btondin/PROJ_CLOCK_16C745/VFDCLK.X/vfd.c

/**
 * =====================================================================
 *  vfd.c — Driver do display VFD IEE Century Series 036X2 (20x2)
 * =====================================================================
 *  Referência: "Specification, VFD, Century Series, Dot Matrix
 *  Modules" (IEE S036X2, rev. N):
 *    - seção 3.2.2.1: interface serial (19200 8N1)
 *    - seção 3.3    : tempos de execução (tabela 3-5) e power-up 500 ms
 *    - seção 4      : códigos de programação usados aqui:
 *        14h  reset por software (limpa tela, modos e atributos)
 *        15h  limpa a tela e leva o cursor ao início ("home")
 *        0Eh  cursor invisível
 *        1Bh  posiciona cursor (2 bytes: 1Bh + ID da posição 0..39)
 *        19h  "Set Address Bit 0 High": em modo serial, equivale a
 *             levantar a linha A0 SOMENTE para o próximo byte — é o
 *             mecanismo para alcançar os códigos 30h..3Fh (seção 4.6)
 *        30h  brilho (3 bytes: 30h, coluna [FFh = todas], nível 0..7)
 *
 *  Por que não há esperas por BUSY: em serial cada byte ocupa 521 us
 *  de linha (19200 baud) e os comandos usados em regime ("Send
 *  Character" e "Cursor Locate") levam ~170 us — o próprio baud rate
 *  serve de flow control. Os comandos lentos (Clear, Reset) só ocorrem
 *  em vfd_iniciar(), que aguarda explicitamente.
 *
 *  A transmissão usa a macro UART_TX (e não a função uart_enviar)
 *  para não gastar níveis da pilha de hardware de 8 posições — as
 *  funções deste driver são chamadas pelo main já no 3º nível.
 * =====================================================================
 */
#include <xc.h>
#include "board.h"
#include "uart.h"
#include "vfd.h"

/* Códigos de controle do IEE 036X2 (A0/RS baixo, seção 4.1)          */
#define VFD_CMD_CURSOR_OFF      0x0Eu
#define VFD_CMD_RESET_SW        0x14u
#define VFD_CMD_LIMPAR_HOME     0x15u
#define VFD_CMD_HOME            0x16u   /* cursor ao início, sem limpar */
#define VFD_CMD_POSICIONAR      0x1Bu
#define VFD_CMD_PREFIXO_A0      0x19u   /* A0=1 só para o próximo byte */
#define VFD_CMD_DEFINIR_UDC     0x18u   /* define caractere (7 bytes)  */

/* Códigos de controle com A0 alto (seção 4.5, exigem prefixo 19h)    */
#define VFD_CMD_BRILHO          0x30u
#define VFD_BRILHO_TODAS_COLS   0xFFu
#define VFD_CMD_BLINK_INICIO    0x31u   /* + código de taxa (2 bytes)  */
#define VFD_CMD_BLINK_FIM       0x32u

/* ------------------------------------------------------------------
 * "Respiro" após o comando de posicionamento (1Bh + posição)
 * ------------------------------------------------------------------
 * O USART do PIC transmite BACK-TO-BACK (o buffer duplo TXREG->TSR
 * emenda um byte no outro, sem intervalo). O display IEE, depois de
 * receber "mover cursor" (1Bh + posição), fica ocupado ~1..1,5 ms
 * executando o movimento e, nesse meio-tempo, PERDE os primeiros
 * caracteres enviados em seguida (ou os marca com '#', o símbolo de
 * erro de recepção — spec 3.2.2.1). Foi por isso que o teste manual
 * pelo PL2303 (bytes digitados com pausas) funcionou e a transmissão
 * contínua do PIC não. Este atraso curto dá tempo ao display antes de
 * mandar os dados. O streaming de caracteres em si aguenta 19200
 * back-to-back (Send Character ~170 us < 521 us/byte).               */
#define VFD_ATRASO_POS_MS   3

#define VFD_IR_PARA(pos)                          \
    do {                                          \
        UART_TX(VFD_CMD_POSICIONAR);              \
        UART_TX((uint8_t)(pos));                  \
        __delay_ms(VFD_ATRASO_POS_MS);            \
    } while (0)

/* ------------------------------------------------------------------
 * CARACTERE PRÓPRIO (UDC) — o sino do indicador de alarme
 * ------------------------------------------------------------------
 * Esta é, BYTE A BYTE, a implementação que já funcionou neste projeto
 * (commit eba5cc2) e que funciona hoje no projeto do PIC18F2550 com
 * ESTE MESMO display. Não "otimizar": não trocar o array por
 * argumentos soltos, não mexer nos valores, não mexer nos tempos.
 *
 * Houve uma tentativa de transformar isto em MACRO com literais
 * imediatos, para poupar um nível da pilha de hardware. Ela produziu
 * um 'D' solto na tela e o comando partido. A suspeita é que a leitura
 * de cada ponto do array (que no PIC16 vem de uma tabela RETLW) INSIRA
 * UM INTERVALO entre os bytes, e que esse intervalo seja requisito, não
 * acidente: o USART é duplo-buffer e, com literais, dois bytes saem
 * emendados sem folga nenhuma.
 *
 * Os 5 bytes seguem o mapeamento entrelaçado da matriz 5x7 da tabela
 * 4-1 do spec (família 35062-01).                                    */

/*      . . # . .        */
/*      . # # # .        */
/*      . # # # .        */
/*      . # # # .   SINO */
/*      # # # # #        */
/*      . . . . .        */
/*      . . # . .        */
static const uint8_t udc_sino[5] = { 0x85u, 0x15u, 0xD4u, 0xEAu, 0x08u };

/* Grava o sino no slot F6h do charset (comando 18h + código + 5 bytes).
 *
 * ATENÇÃO: este é um comando MULTIBYTE de 7 bytes, e o spec (seção 4.1,
 * CAUTION) avisa que erro em comando multibyte faz o firmware do display
 * "pular" para fora do modo de controle — foi exatamente o que travava o
 * menu de brilho antes dos respiros. Daí os __delay_ms aqui.
 *
 * Se na bancada aparecer 'v' no lugar do sino, o display está truncando
 * o bit 7 (F6h -> 76h = 'v'); nesse caso o spec oferece o código 17h
 * ("Set Data Bit 7 High") como prefixo para o byte seguinte.
 *
 * PROFUNDIDADE DE PILHA: esta função é chamada DIRETAMENTE pelo main, e
 * não de dentro de vfd_iniciar() como em eba5cc2. O fluxo de bytes é o
 * mesmo — só muda quem chama. O motivo é medido: ler udc_sino[i] emite a
 * chamada escondida para a tabela RETLW e, aninhada sob vfd_iniciar(),
 * essa leitura batia EXATAMENTE nos 8 níveis da pilha de hardware, que é
 * a condição que derrubava o firmware. Chamada do main ela fica em 7,
 * com um nível de folga.                                              */
void vfd_definir_sino(void)
{
    uint8_t i;

    UART_TX(VFD_CMD_DEFINIR_UDC);
    UART_TX(VFD_CHAR_SINO);
    __delay_ms(VFD_ATRASO_POS_MS);      /* respiro após o cabeçalho    */
    for (i = 0; i < 5u; i++) {
        UART_TX(udc_sino[i]);
    }
    __delay_ms(VFD_ATRASO_POS_MS);      /* respiro antes do próximo cmd */
}

void vfd_iniciar(void)
{
    /* O spec (3.3) exige >= 500 ms após a alimentação antes do
     * primeiro comando ("Processor Power-up Cycle").                 */
    ESPERAR_MS(500);

    /* Reset por software: tela limpa, cursor no início, modos padrão
     * (rolagem vertical, charset europeu, brilho máximo).
     * A tabela 3-5 diz que o reset executa em ~0,8 ms, mas damos
     * folga larga: é uma operação única no boot, e um reset ainda em
     * curso engoliria os comandos seguintes.                         */
    UART_TX(VFD_CMD_RESET_SW);
    ESPERAR_MS(100);

    /* Limpa e leva o cursor ao início (estado conhecido)             */
    UART_TX(VFD_CMD_LIMPAR_HOME);
    __delay_ms(10);

    /* Cursor invisível. ATENÇÃO: o padrão de fábrica é cursor LIGADO
     * piscando a 4 Hz (spec 4.2, código 0Fh) — sem este comando fica
     * um caractere piscando na tela, parecendo um editor de texto.   */
    UART_TX(VFD_CMD_CURSOR_OFF);
    __delay_ms(10);

    /* Nota sobre a ROLAGEM VERTICAL: o modo padrão do display é rolar
     * para cima quando a última linha enche (spec 4.3). Tentamos travar
     * isso pelo comando 10h ("Scroll Line Lock"), mas ele NÃO teve
     * efeito confiável neste exemplar (o conteúdo continuava subindo, e
     * a 2ª linha nunca era usada). A solução adotada é outra e não
     * depende desse comando: o desenho de tela (vfd_quadro) escreve as
     * DUAS linhas como um único fluxo de 40 caracteres a partir do topo,
     * deixando o auto-wrap encher a 2ª linha; como nunca se envia um 41º
     * caractere, a rolagem jamais é disparada. Ver vfd_quadro().       */

}

void vfd_limpar(void)
{
    UART_TX(VFD_CMD_LIMPAR_HOME);
}

void vfd_reafirmar(void)
{
    /* Reestabelece um estado conhecido ANTES do redesenho completo do
     * refresco periódico de auto-correção:
     *   - 0Eh: cursor invisível (caso ruído tenha reativado o cursor);
     *   - 16h: cursor ao início ("home") — re-sincroniza a posição
     *     interna do display sem limpar a tela.
     * Não limpa a tela (o conteúdo é reescrito por cima em seguida),
     * então o refresco NÃO pisca. Os respiros pós-comando evitam que o
     * display perca o byte seguinte (mesmo motivo do VFD_IR_PARA).     */
    UART_TX(VFD_CMD_CURSOR_OFF);
    __delay_ms(VFD_ATRASO_POS_MS);
    UART_TX(VFD_CMD_HOME);
    __delay_ms(VFD_ATRASO_POS_MS);
}

void vfd_cursor(uint8_t linha, uint8_t coluna)
{
    /* Posições numeradas 0..39: linha 0 = 0..19, linha 1 = 20..39.   */
    VFD_IR_PARA(coluna + ((linha != 0u) ? VFD_COLUNAS : 0u));
}

void vfd_escrever_char(char c)
{
    /* Caracteres < 20h são códigos de controle: filtra por segurança
     * para nunca disparar um comando sem querer no meio de um texto. */
    if ((uint8_t)c < 0x20u) {
        c = ' ';
    }
    UART_TX((uint8_t)c);
}

void vfd_escrever_texto(const char *texto)
{
    while (*texto != '\0') {
        vfd_escrever_char(*texto);
        texto++;
    }
}

/* ------------------------------------------------------------------
 * vfd_quadro — desenha as DUAS linhas como um único fluxo de 40 chars
 * ------------------------------------------------------------------
 * Este é o coração do driver e a correção definitiva do bug em que
 * "tudo caía na 1ª linha e a 2ª nunca era usada". Em vez de posicionar
 * cada linha (um 1Bh no MEIO do fluxo, que embaralhava a rolagem),
 * reposiciona UMA única vez no canto superior esquerdo (1Bh 00h — o
 * mesmo comando que o teste manual confirmou levar 'A' ao topo-esquerda)
 * e despeja 40 caracteres seguidos. O auto-wrap do display quebra
 * sozinho no 21º caractere, enchendo a 2ª linha; o 40º ocupa a última
 * célula SEM rolar, porque só um 41º caractere dispararia a rolagem
 * vertical. É, byte a byte, a mesma sequência que funcionou no terminal.
 *
 * Loops INLINE de propósito (função-folha: só a macro UART_TX): não
 * gasta nível da pilha de hardware de 8 posições, que o laço divide com
 * a ISR de USB. Cada ponteiro pode ter MENOS de VFD_COLUNAS caracteres —
 * o restante é completado com espaços (apaga a escrita anterior sem
 * "clear", logo sem piscar).
 * ------------------------------------------------------------------ */
void vfd_quadro(const char *linha0, const char *linha1)
{
    uint8_t i;
    uint8_t c;

    VFD_IR_PARA(0);                        /* canto superior esquerdo  */

    for (i = 0; i < VFD_COLUNAS; i++) {    /* linha 0 (20 caracteres)  */
        if (*linha0 != '\0') {
            c = (uint8_t)*linha0++;
            if (c < 0x20u) { c = ' '; }    /* nunca vazar controle     */
        } else {
            c = ' ';                        /* completa com espaços     */
        }
        UART_TX(c);
    }
    for (i = 0; i < VFD_COLUNAS; i++) {    /* linha 1 (por auto-wrap)  */
        if (*linha1 != '\0') {
            c = (uint8_t)*linha1++;
            if (c < 0x20u) { c = ' '; }
        } else {
            c = ' ';
        }
        UART_TX(c);
    }
}

void vfd_quadro_piscante(const char *linha0, const char *linha1, uint8_t taxa)
{
    uint8_t i;
    uint8_t c;

    VFD_IR_PARA(0);

    /* Liga o atributo piscante ANTES da linha 0 e desliga DEPOIS: só a
     * linha de cima pisca (31h/32h delimitam a faixa de caracteres). O
     * respiro pós-comando evita que o display perca o 1º caractere.    */
    UART_TX(VFD_CMD_PREFIXO_A0);
    UART_TX(VFD_CMD_BLINK_INICIO);
    UART_TX(taxa);
    __delay_ms(VFD_ATRASO_POS_MS);
    for (i = 0; i < VFD_COLUNAS; i++) {
        if (*linha0 != '\0') {
            c = (uint8_t)*linha0++;
            if (c < 0x20u) { c = ' '; }
        } else {
            c = ' ';
        }
        UART_TX(c);
    }
    UART_TX(VFD_CMD_PREFIXO_A0);
    UART_TX(VFD_CMD_BLINK_FIM);
    for (i = 0; i < VFD_COLUNAS; i++) {
        if (*linha1 != '\0') {
            c = (uint8_t)*linha1++;
            if (c < 0x20u) { c = ' '; }
        } else {
            c = ' ';
        }
        UART_TX(c);
    }
}

void vfd_campo_bcd(uint8_t linha, uint8_t coluna, uint8_t novo, uint8_t antigo)
{
    /* linha * 20 escrito como (linha*16 + linha*4). A multiplicação
     * normal chamaria ___bmul, e cada chamada custa um nível da pilha
     * de hardware de 8 posições que o main divide com a ISR do USB —
     * ver a nota de PROFUNDIDADE DE PILHA em main.c. Deslocamentos por
     * constante viram instruções, não chamadas.                      */
    uint8_t base = (uint8_t)(coluna + ((linha != 0u) ? VFD_COLUNAS : 0u));

    /* Reescreve SÓ os dígitos que realmente mudaram. Num relógio, de
     * um segundo para o outro quase sempre muda apenas a unidade dos
     * segundos: 1 caractere em vez de 8. Menos escrita = menos tempo
     * com a tela sendo alterada = sem piscada perceptível.
     *
     * Função-FOLHA de propósito (só usa a macro UART_TX, não chama
     * ninguém): economiza um nível da pilha de hardware de 8 níveis,
     * que o main divide com a ISR do USB.                            */
    if (novo == antigo) {
        return;                      /* nada mudou: nem posiciona     */
    }

    if ((novo >> 4) != (antigo >> 4)) {
        /* A dezena mudou: manda os dois dígitos de uma vez (4 bytes,
         * mais barato que dois posicionamentos separados).           */
        VFD_IR_PARA(base);
        UART_TX((uint8_t)('0' + (novo >> 4)));
        UART_TX((uint8_t)('0' + (novo & 0x0Fu)));
    } else {
        /* Só a unidade mudou: 1 caractere (3 bytes no total).        */
        VFD_IR_PARA(base + 1u);
        UART_TX((uint8_t)('0' + (novo & 0x0Fu)));
    }
}

void vfd_piscar_inicio(uint8_t taxa)
{
    /* Seção 4.5: 31h marca o INÍCIO do trecho piscante — os caracteres
     * escritos DEPOIS deste comando é que piscam, até virem um 32h ou
     * serem sobrescritos por texto normal.                           */
    UART_TX(VFD_CMD_PREFIXO_A0);
    UART_TX(VFD_CMD_BLINK_INICIO);
    UART_TX(taxa);
}

void vfd_piscar_fim(void)
{
    UART_TX(VFD_CMD_PREFIXO_A0);
    UART_TX(VFD_CMD_BLINK_FIM);
}

void vfd_brilho(uint8_t nivel)
{
    if (nivel > VFD_BRILHO_MINIMO) {
        nivel = VFD_BRILHO_MINIMO;
    }
    /* Em serial, o código 30h (A0 alto) é alcançado com o prefixo
     * 19h (seção 4.6). O comando é MULTIBYTE: 30h + coluna + nível.
     *
     * ATENÇÃO (era o bug do "menu de brilho trava tudo"): o datasheet
     * (seção 4.1, CAUTION) diz que ERRO em comando multibyte faz o
     * firmware do display "pular" para fora do modo de controle. Como o
     * display fica ocupado logo após o código de comando (mesma coisa
     * que já derrubava bytes depois do 1Bh de posição), sem um respiro
     * ele perdia o parâmetro seguinte; a cada toque no botão a corrupção
     * se acumulava até travar o display. Os __delay_ms abaixo dão tempo
     * ao display digerir o comando e o parâmetro (o PIC não trava — só
     * o parser do display se perdia).
     *
     * Sobre "não mudava o brilho": sem potenciômetro externo no pino
     * DIMMING (só o pull-up interno de 10k), o limite de HARDWARE fica
     * no brilho máximo, então o software cobre todos os 8 níveis
     * 00h(máx)..07h(mín).                                             */
    UART_TX(VFD_CMD_PREFIXO_A0);          /* 19h                        */
    UART_TX(VFD_CMD_BRILHO);              /* 30h (código de comando)    */
    __delay_ms(VFD_ATRASO_POS_MS);        /* respiro: display digere    */
    UART_TX(VFD_BRILHO_TODAS_COLS);       /* FFh = todas as colunas     */
    UART_TX(nivel);                       /* 0 = máximo .. 7 = mínimo   */
    __delay_ms(VFD_ATRASO_POS_MS);        /* respiro antes do próximo cmd */
}
