btondin/PROJ_CLOCK_16C745/VFDCLK.X/vfd.h

/**
 * =====================================================================
 *  vfd.h — Driver do display VFD IEE Century Series 036X2 (20x2)
 * =====================================================================
 *  Interface: SERIAL 19200 baud 8N1 (jumper de personalidade do módulo
 *  em 19200 — ver HARDWARE/pinagem.md).
 *
 *  Em modo serial o display é somente-escrita (o spec proíbe leitura),
 *  e não há linha BUSY: o handshake é garantido por aritmética — a
 *  19200 baud um caractere ocupa 521 us na linha, e os comandos que
 *  este driver usa em regime executam bem abaixo disso (tabela 3-5 do
 *  spec S036X2): "Send Character" e "Cursor Locate" levam ~170 us tanto
 *  no 2x20 quanto no 2x40. Ou seja, o display sempre termina antes do
 *  próximo byte chegar.
 *
 *  EXCEÇÕES que NÃO cabem em 521 us e por isso levam espera explícita
 *  no código: "Clear" (410 us no 2x20, 715 us no 2x40) e "Reset"
 *  (~800 us) — ambos só acontecem em vfd_iniciar(), que já aguarda.
 * =====================================================================
 */
#ifndef VFD_H
#define VFD_H

#include <stdint.h>

#define VFD_COLUNAS  20u
#define VFD_LINHAS   2u

/* Níveis de brilho do 036X2: 0 = máximo ... 7 = mínimo (spec 4.5).   */
#define VFD_BRILHO_MAXIMO   0u
#define VFD_BRILHO_MINIMO   7u

/* ------------------------------------------------------------------
 * CARACTERES DEFINIDOS PELO USUÁRIO (UDC)
 * ------------------------------------------------------------------
 * O 036X2 permite redefinir posições altas da tabela (comando 18h,
 * seção 4.4). Depois de definidos, basta escrever o código como se
 * fosse um caractere normal — vfd_quadro() deixa passar tudo acima de
 * 20h, então eles entram no fluxo das telas sem tratamento especial.
 * ------------------------------------------------------------------ */
#define VFD_CHAR_SINO   0xF6u   /* sino: alarme habilitado            */

/* Liga/desliga a gravação do sino no boot. Em 0, o indicador de alarme
 * cai para '*' (ver main.c). Serve para isolar o comando 18h caso ele
 * volte a dar problema — foi assim que o resto do firmware pôde ser
 * depurado enquanto o sino estava fora.                              */
#define USAR_SIMBOLOS_PROPRIOS  1

/* ------------------------------------------------------------------
 * CARACTERES NATIVOS DA FONTE deste módulo
 * ------------------------------------------------------------------
 * Estes NÃO são UDC: já existem na tabela do display, então não gastam
 * um slot de caractere próprio nem um comando no boot. Foram
 * localizados na bancada com um navegador de fonte temporário, que
 * mostrava 16 códigos por vez e foi removido depois.
 * ------------------------------------------------------------------ */
#define VFD_CHAR_GRAU_NATIVO  0xB9u   /* símbolo de grau, para "°C"   */

/* Grava o sino no charset do display. Chamar DEPOIS de vfd_iniciar():
 * o reset por software (14h) restaura os modos padrão e apagaria a
 * definição feita antes dele. É chamada pelo main, e não de dentro do
 * vfd_iniciar(), por causa da pilha — ver a nota em vfd.c.           */
void vfd_definir_sino(void);

/* Reinicializa o display (reset por software) e o deixa limpo, com
 * cursor invisível e rolagem vertical padrão. Aguarda os 500 ms de
 * power-up exigidos pelo spec (seção 3.3) antes de falar com ele.    */
void vfd_iniciar(void);

/* Apaga a tela e leva o cursor para a posição inicial (código 15h).  */
void vfd_limpar(void);

/* Reafirma um estado conhecido (cursor invisível + cursor no início)
 * SEM limpar a tela. Usada no refresco periódico de auto-correção,
 * logo antes de um redesenho completo — cura desvios de modo/posição
 * causados por ruído, sem piscar.                                    */
void vfd_reafirmar(void);

/* Posiciona o cursor. linha: 0..1, coluna: 0..19 (comando 1Bh + ID,
 * posições numeradas da esquerda p/ direita, de cima p/ baixo).      */
void vfd_cursor(uint8_t linha, uint8_t coluna);

/* Escreve um caractere ASCII imprimível na posição atual do cursor.  */
void vfd_escrever_char(char c);

/* Escreve uma string C (terminada em '\0') a partir do cursor atual. */
void vfd_escrever_texto(const char *texto);

/* Desenha as DUAS linhas de uma vez, como um ÚNICO fluxo de 40
 * caracteres a partir do canto superior esquerdo, deixando o AUTO-WRAP
 * do display levar do fim da linha 0 ao início da linha 1. É o método
 * que o teste manual comprovou (40 caracteres seguidos enchem as duas
 * linhas) e que NÃO dispara a rolagem vertical — só um 41º caractere
 * rolaria. Cada ponteiro pode ter menos de VFD_COLUNAS: o driver
 * completa a linha com espaços. É a forma canônica de (re)desenhar uma
 * tela inteira neste projeto.                                        */
void vfd_quadro(const char *linha0, const char *linha1);

/* Igual a vfd_quadro(), mas a LINHA 0 pisca (atributo 31h/32h do
 * display, sem custo de tráfego serial). Usada na tela do alarme
 * disparado.                                                         */
void vfd_quadro_piscante(const char *linha0, const char *linha1, uint8_t taxa);

/* Atualiza um campo de DOIS DÍGITOS BCD (ex.: "07") escrevendo apenas
 * o(s) dígito(s) que mudaram entre 'antigo' e 'novo'. Se nada mudou,
 * não envia byte nenhum. É o que mantém o relógio sem piscar: na
 * maioria dos segundos só a unidade muda -> 1 caractere reescrito.   */
void vfd_campo_bcd(uint8_t linha, uint8_t coluna, uint8_t novo, uint8_t antigo);

/* Ajusta o brilho de toda a tela: 0 (máximo) a 7 (mínimo).
 * Sequência serial: 19h (A0 alto p/ próximo byte) 30h FFh nível.     */
void vfd_brilho(uint8_t nivel);

/* Taxas de piscada aceitas pelo 036X2 (spec 4.5, código 31h)         */
#define VFD_BLINK_DESLIGA   0x00u
#define VFD_BLINK_1HZ       0x01u
#define VFD_BLINK_2HZ       0x02u
#define VFD_BLINK_4HZ       0x04u

/* Liga o atributo "piscante" para os caracteres escritos A PARTIR
 * daqui (usado na tela de alarme). Chamar vfd_piscar_fim() depois.   */
void vfd_piscar_inicio(uint8_t taxa);

/* Encerra o trecho piscante iniciado por vfd_piscar_inicio().        */
void vfd_piscar_fim(void);

#endif /* VFD_H */
